ricardoquesada/unijoysticle2/board/unijoysticle2plus/unijoysticle2plus.png

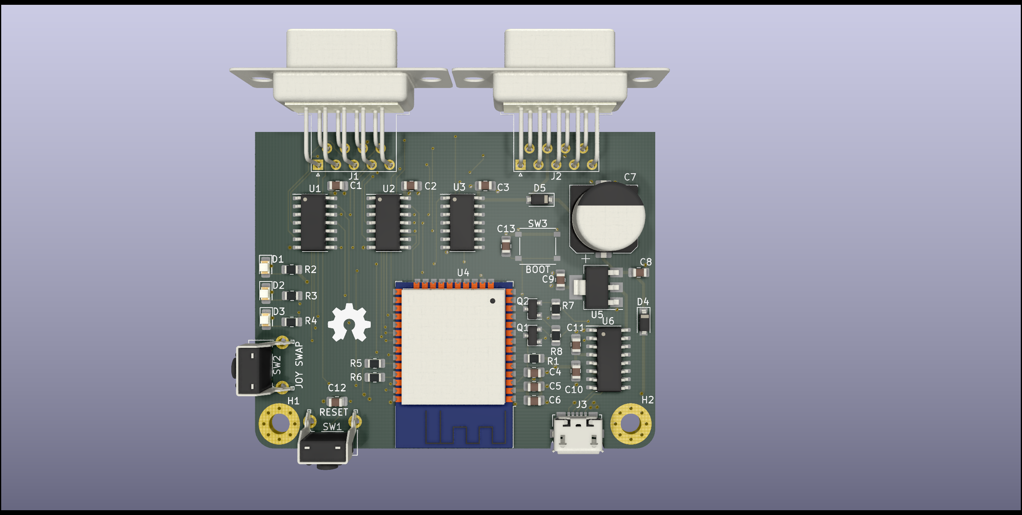
board/unijoysticle2plus/unijoysticle2plus.png
